matiRLC/NixieClock/docs/16MHz UBRRn Setting.png

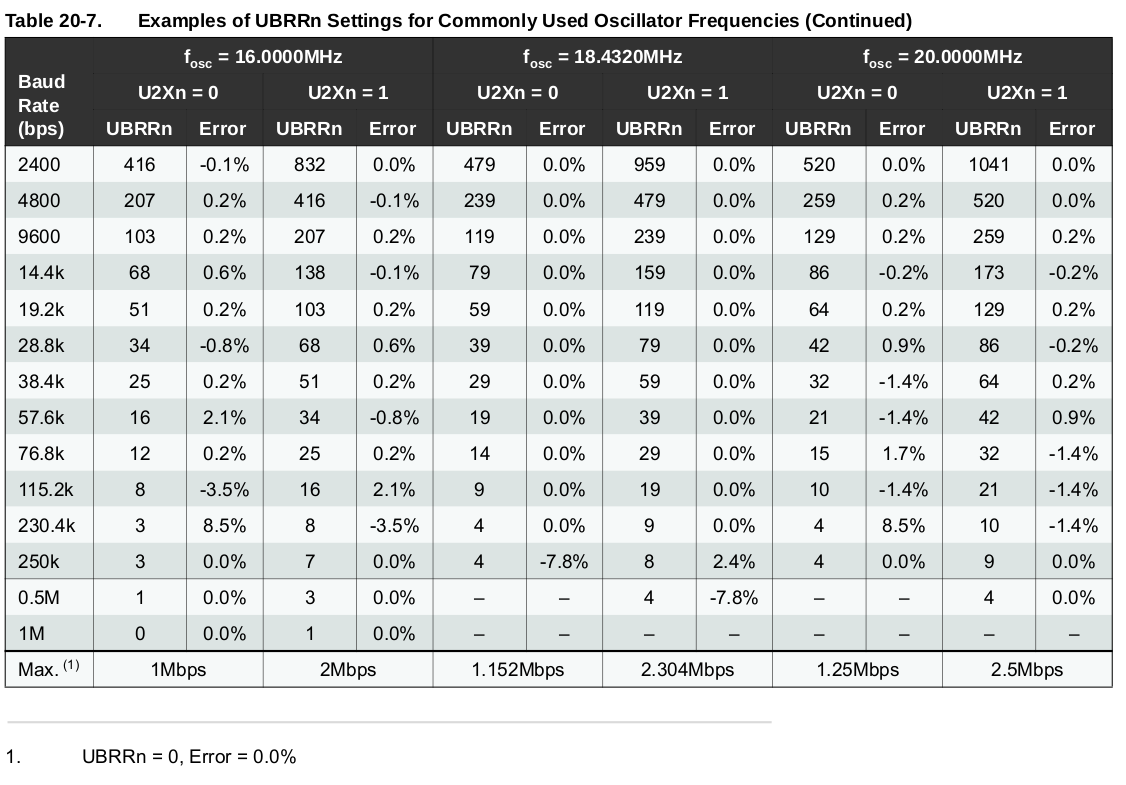
docs/16MHz UBRRn Setting.png
