matiRLC/NixieClock/docs/IMG_20170116_235412.jpg

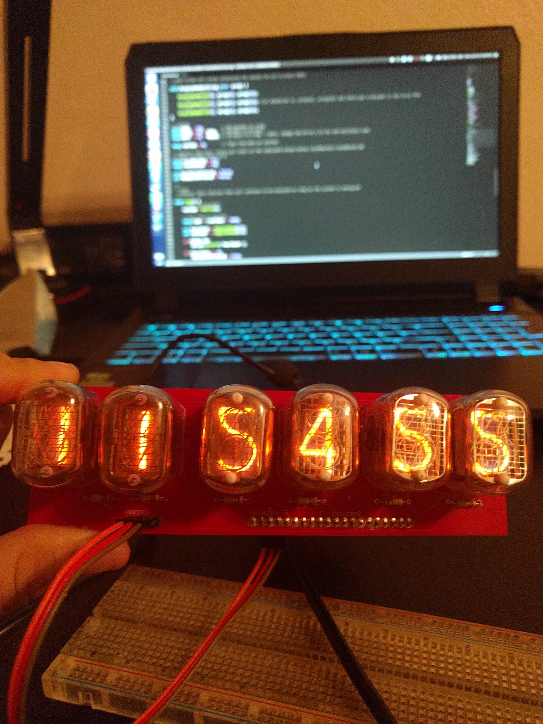
docs/IMG_20170116_235412.jpg
