matiRLC/NixieClock/docs/IMG_20170116_235456_415.jpg

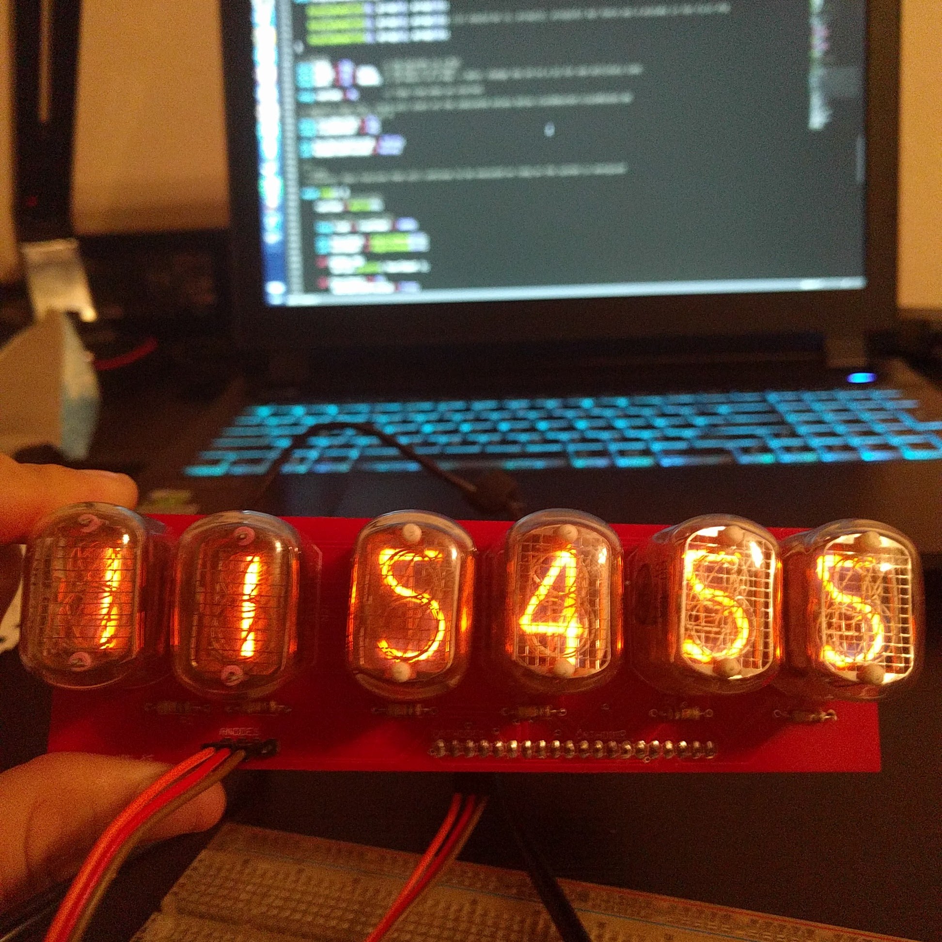
docs/IMG_20170116_235456_415.jpg
