matiRLC/NixieClock/docs/nixieclock1.jpg

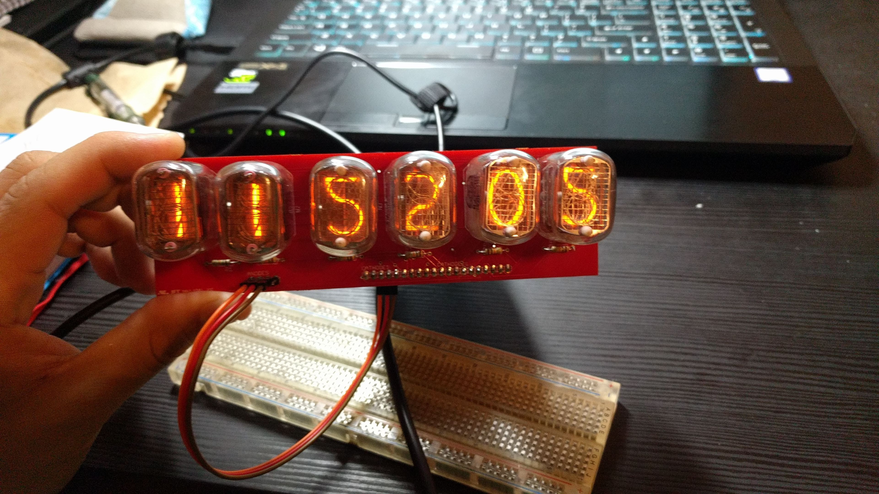
docs/nixieclock1.jpg
