matiRLC/NixieClock/docs/nixieclock2.jpg

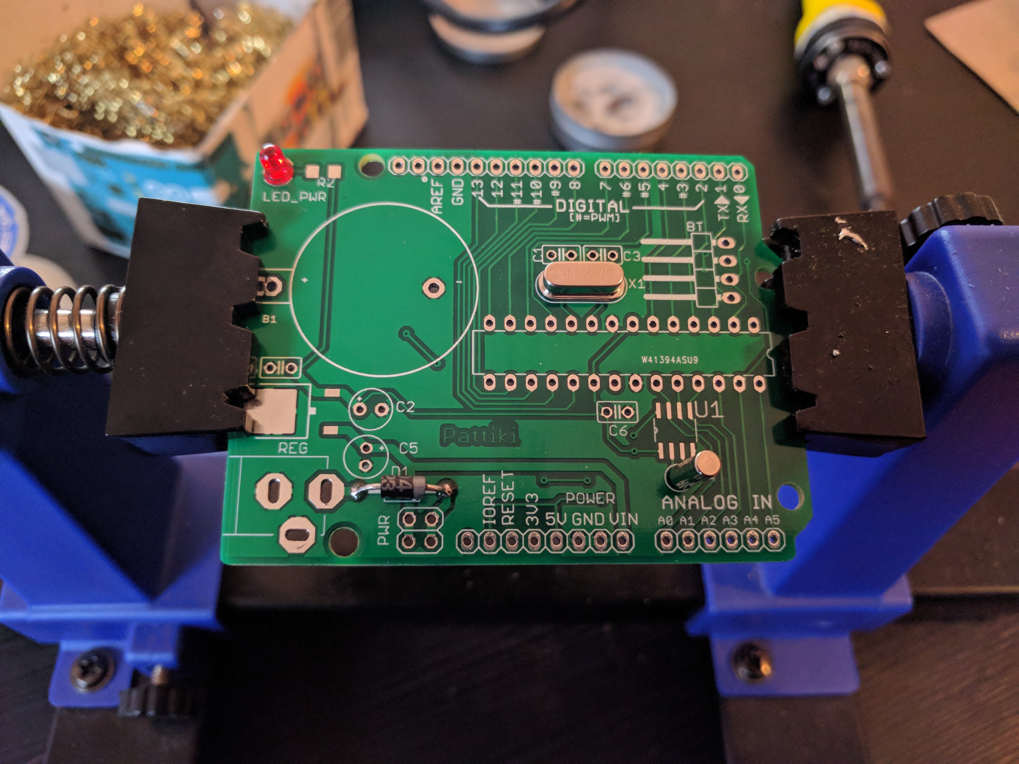
docs/nixieclock2.jpg
