matiRLC/NixieClock/docs/nixieclock3.jpg

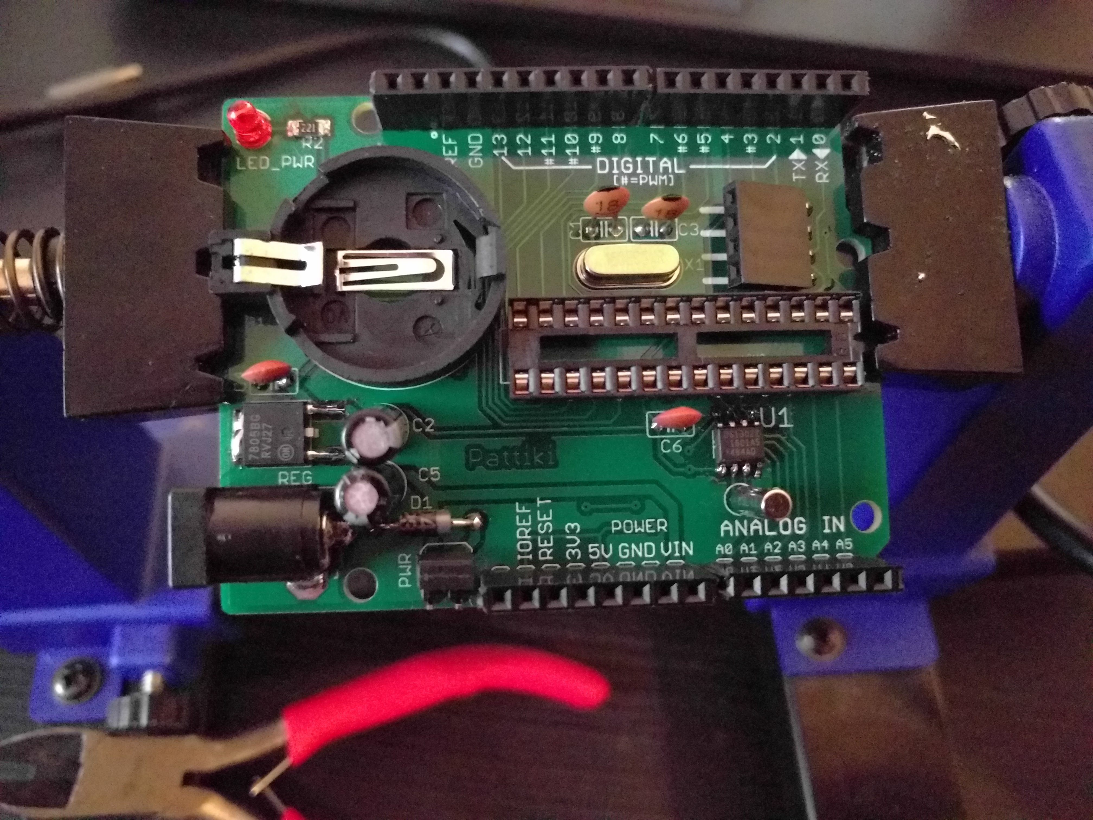
docs/nixieclock3.jpg
