matiRLC/NixieClock/docs/nixieclock6.jpg

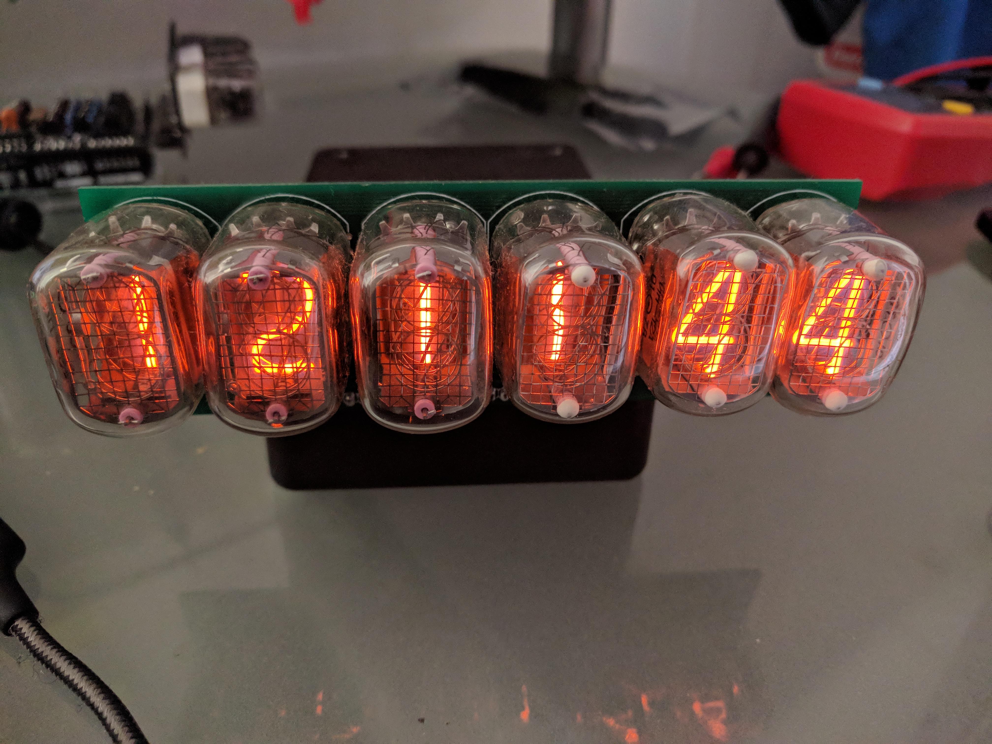
docs/nixieclock6.jpg
